joshajohnson/sea-picro/documentation/prod/ext-bot.JPG

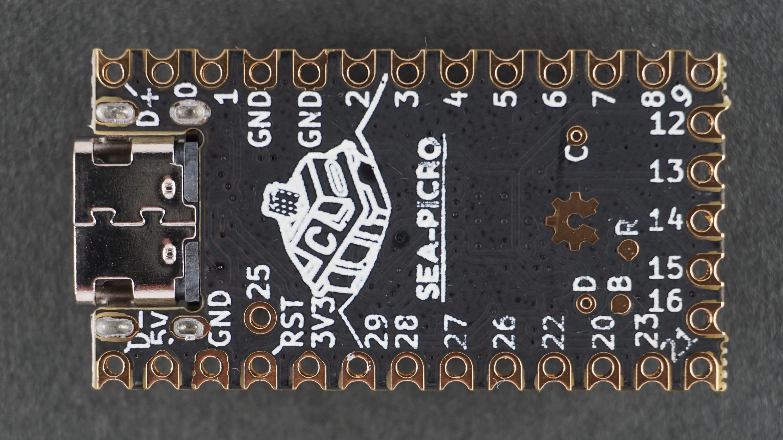
documentation/prod/ext-bot.JPG
