joshajohnson/sea-picro/documentation/prod/rst-back.JPG

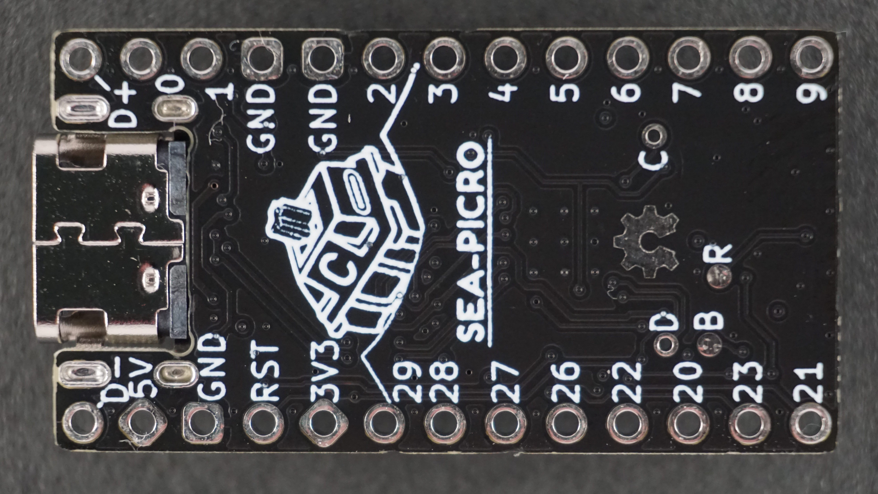
documentation/prod/rst-back.JPG
