joshajohnson/sea-picro/documentation/renders/SEA-PICRO Front Solo.jpg

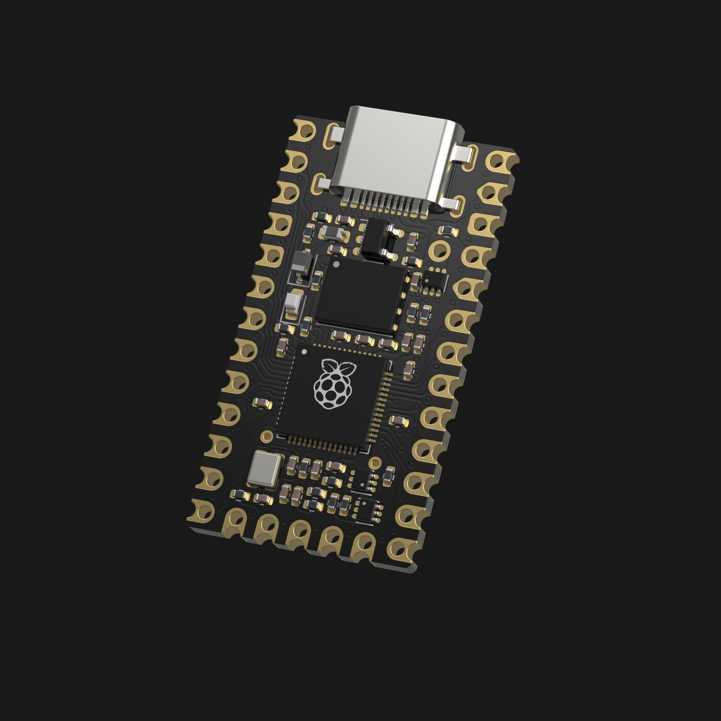
documentation/renders/SEA-PICRO Front Solo.jpg
