joshajohnson/sea-picro/documentation/renders/SEA-PICRO Pair Iso.jpg

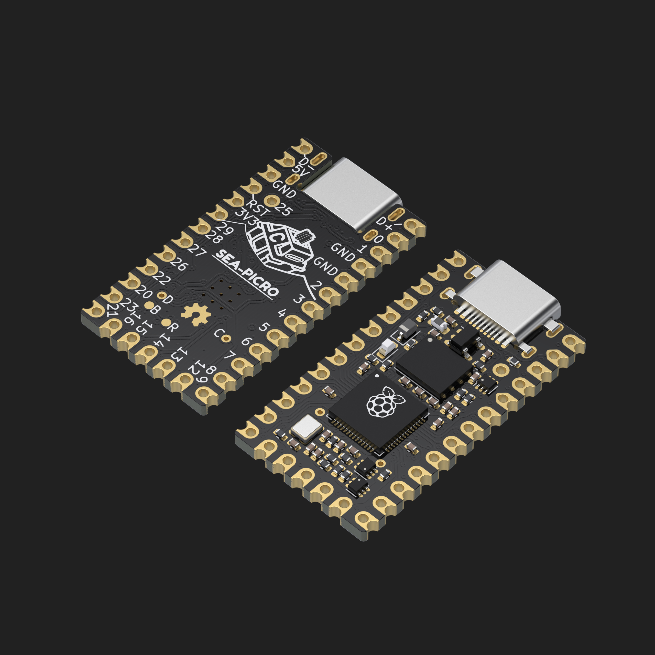
documentation/renders/SEA-PICRO Pair Iso.jpg
