joshajohnson/sea-picro/documentation/sea-picro-ext-bot.JPG

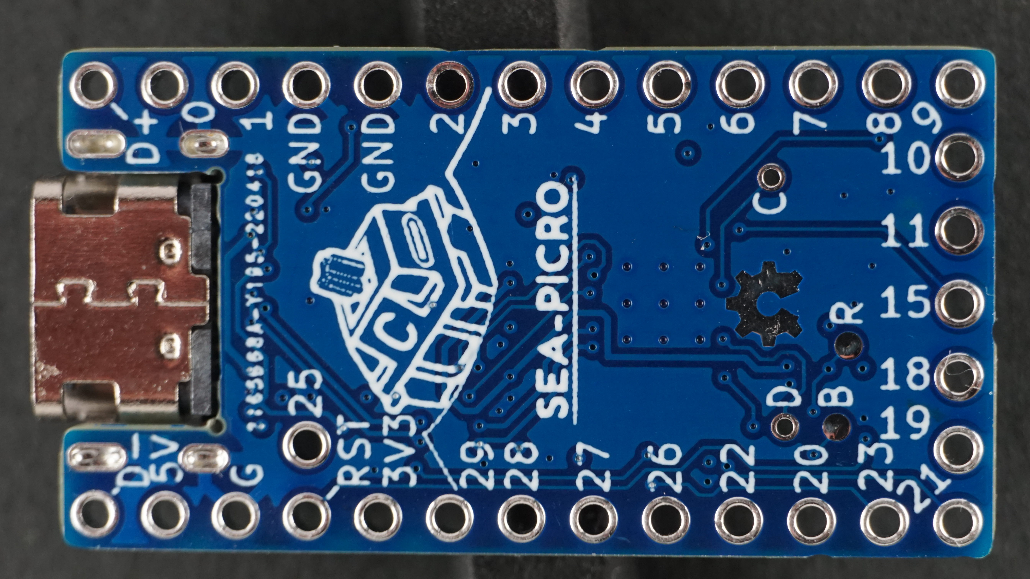
documentation/sea-picro-ext-bot.JPG
