joshajohnson/sea-picro/documentation/sea-picro-ext-top.JPG

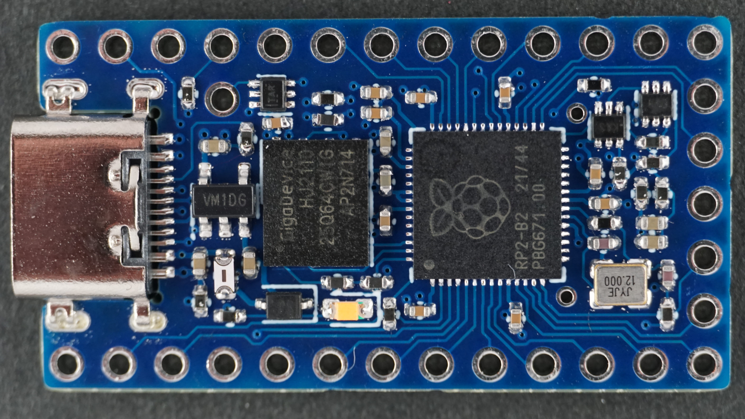
documentation/sea-picro-ext-top.JPG
