joshajohnson/sea-picro/documentation/sea-picro-rst-top.JPG

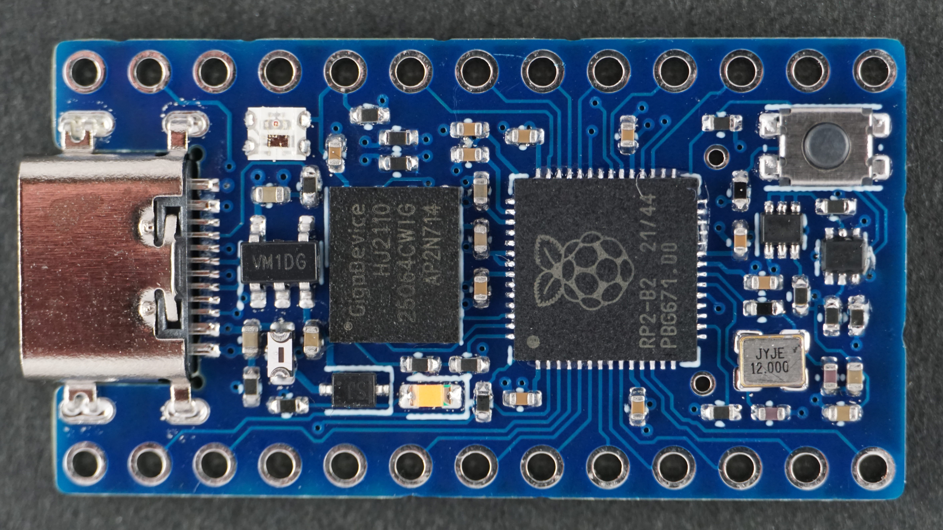
documentation/sea-picro-rst-top.JPG
