joshajohnson/sea-picro/simulation/hold-close-up.png

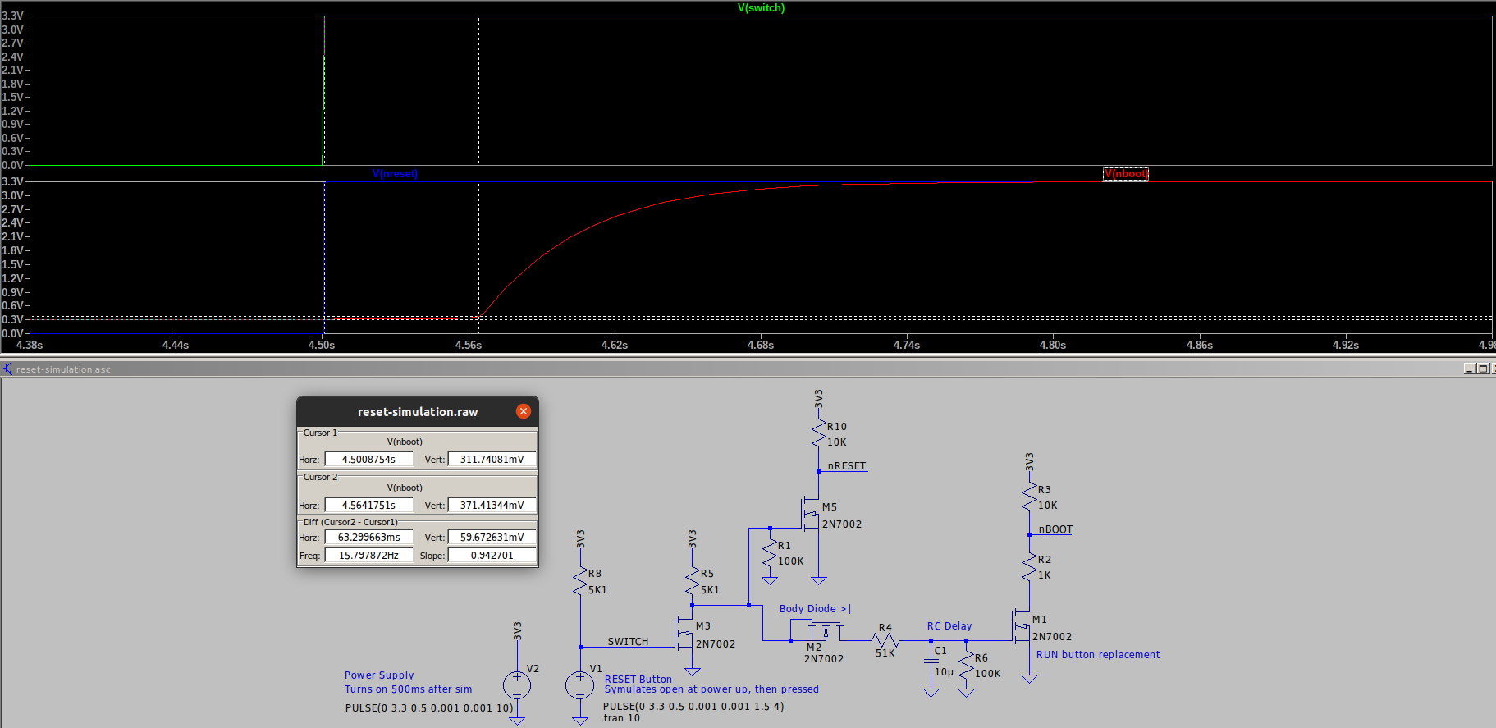
simulation/hold-close-up.png
