joshajohnson/sea-picro/simulation/hold.png

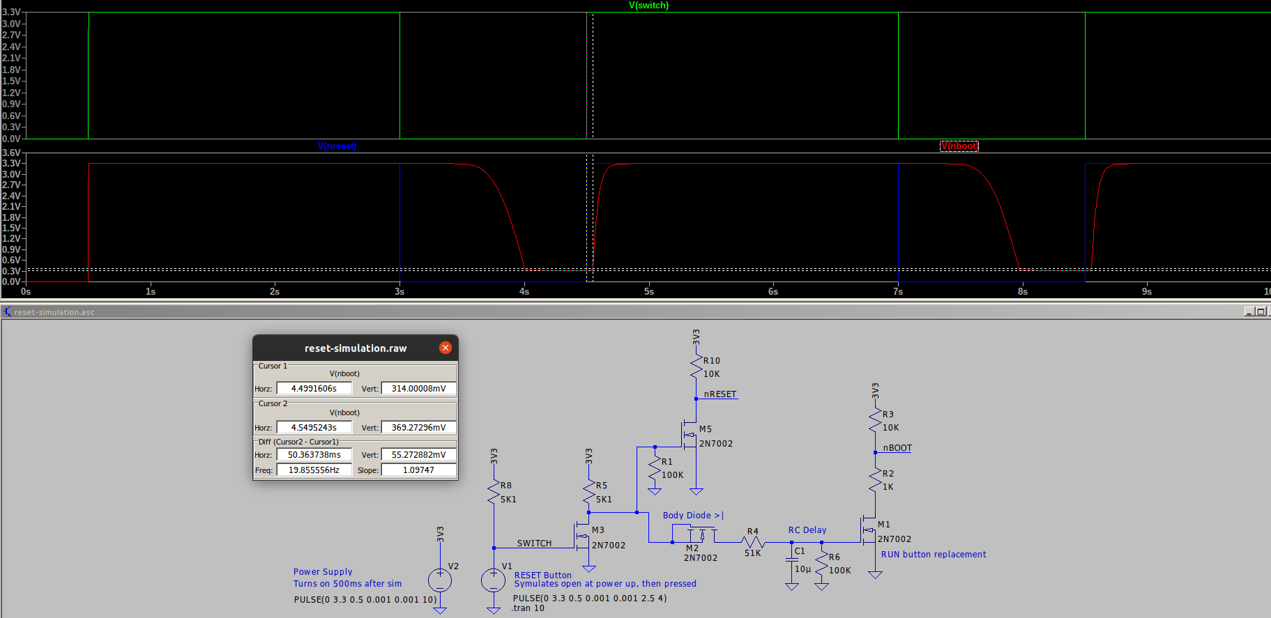
simulation/hold.png
