joshajohnson/sea-picro/simulation/tap.png

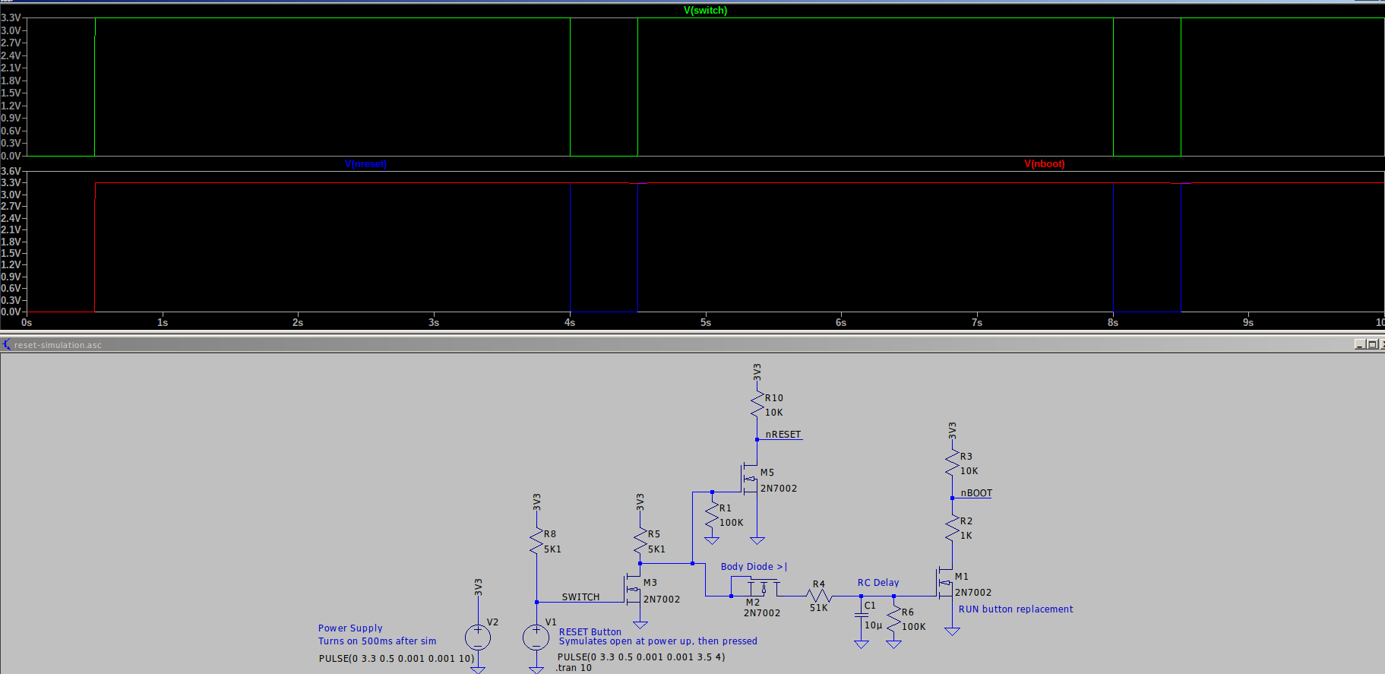
simulation/tap.png
