joshajohnson/sea-picro/simulation/reset-simulation.asc

C1: cap; 10µ
M1: nmos; 2N7002
M2: nmos; 2N7002
M3: nmos; 2N7002
M5: nmos; 2N7002
R2: res; 1K
R3: res; 10K
R4: res; 51K
R5: res; 5K1
R6: res; 100K
R8: res; 5K1
R10: res; 5K1
V1: voltage; PULSE(3.3 0 0.6 0.001 0.001 1.5 5)
V2: voltage; PULSE(0 3.3 0.5 0.001 0.001 10)
Named nets: 0, 3V3, nBOOT, SWITCH, nRESET
RESET Button
.tran 10
RUN button replacement
Body Diode >|
RC Delay
Power Supply
Turns on 500ms after sim
Symulates open at power up, then pressed
